furpectfox/LiPo-Powered_Analog_LED_Driver/images/low-pass_filter.png

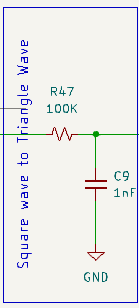
images/low-pass_filter.png
